Sn3akySqu1d/PuzzleClock/Images/image-4.png

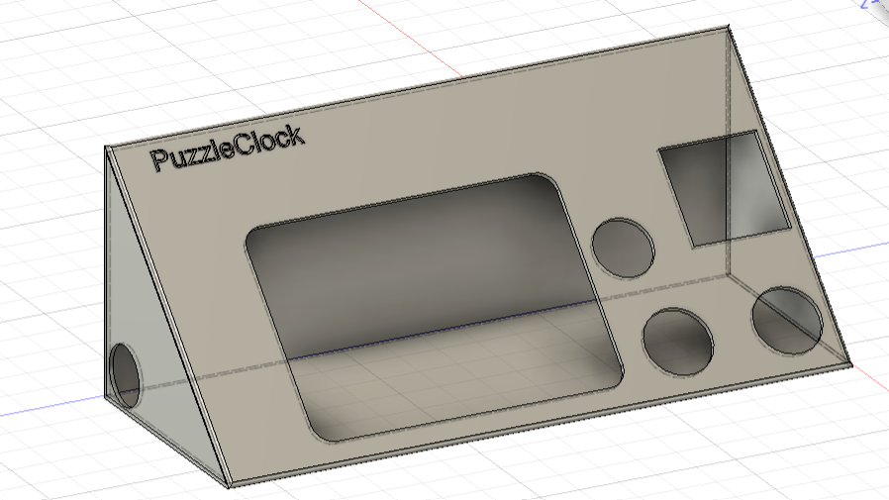
Images/image-4.png
