Sn3akySqu1d/PuzzleClock/Images/image-5.png

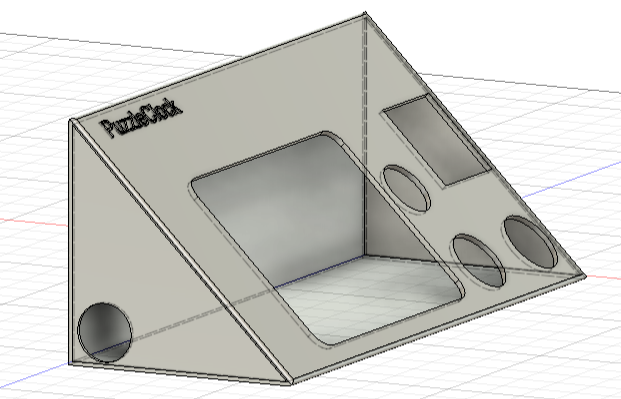
Images/image-5.png
