Sn3akySqu1d/PuzzleClock/Images/image-6.png

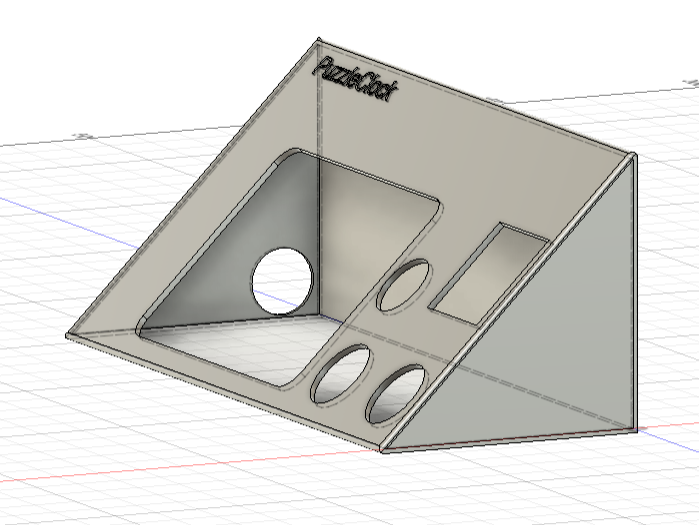
Images/image-6.png
