Sn3akySqu1d/PuzzleClock/Kicad/clock.kicad_sch

## KiCad design Kicad/clock.kicad_sch (2025-08-01)

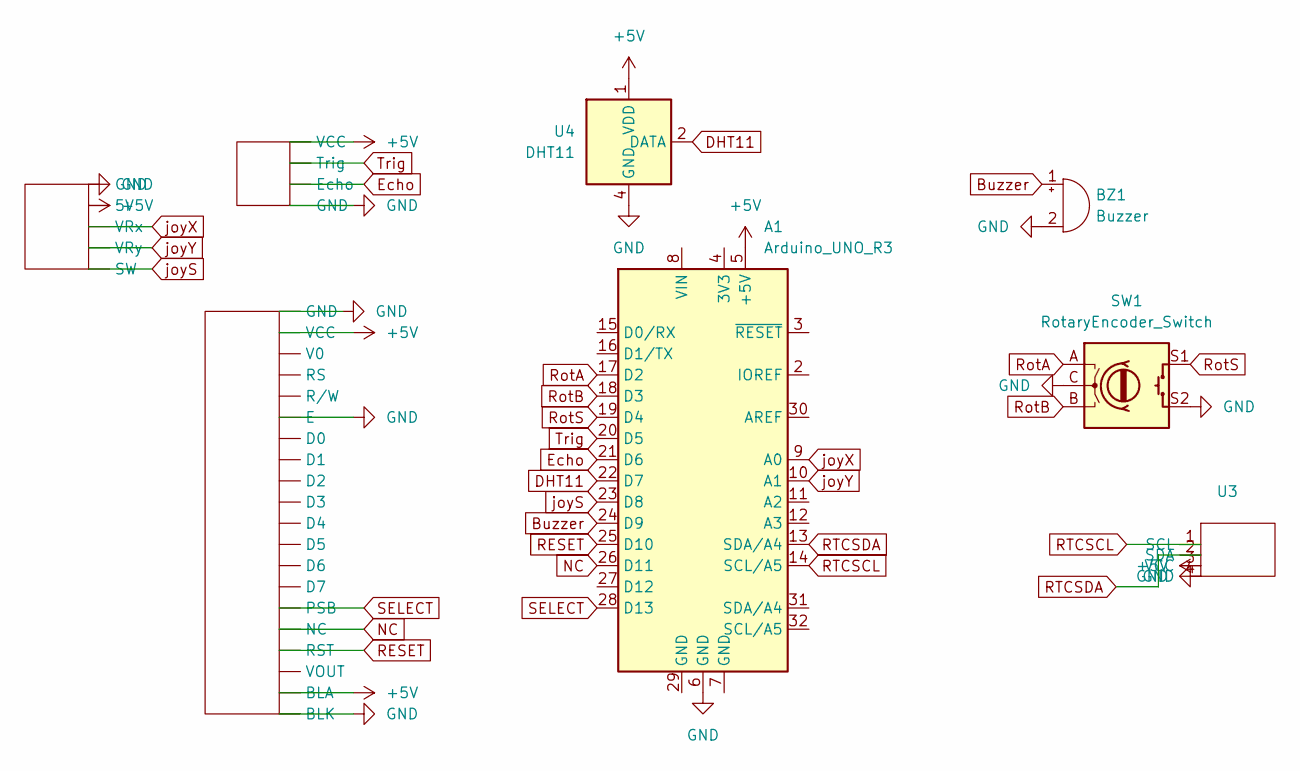
[picture p14: schematic clock.kicad_sch]

Parts:
A1: Arduino_UNO_R3
BZ1: Buzzer
SW1: RotaryEncoder_Switch
U1, U2, U3, U5: (no value)
U4: DHT11; Aosong_DHT11_5.5x12.0_P2.54mm

Connections:
+5V: A1.5 (+5V), U1., U2., U3.3 (VCC), U4.1 (VDD), U5.
Buzzer: A1.24 (D9), BZ1.1 (+)
DHT11: A1.22 (D7), U4.2 (DATA)
Echo: A1.21 (D6), U2.
GND: A1.6 (GND), BZ1.2 (-), SW1.C, SW1.S2, U1., U2., U3.4 (GND), U4.4 (GND), U5.
NC: A1.26 (D11), U1.
RESET: A1.25 (D10), U1.
RTCSCL: A1.14 (SCL/A5), U3.1 (SCL)
RTCSDA: A1.13 (SDA/A4), U3.2 (SDA)
RotA: A1.17 (D2), SW1.A
RotB: A1.18 (D3), SW1.B
RotS: A1.19 (D4), SW1.S1
SELECT: A1.28 (D13), U1.
Trig: A1.20 (D5), U2.
joyS: A1.23 (D8), U5.
joyX: A1.9 (A0), U5.
joyY: A1.10 (A1), U5.
